tobychui/The-3D-Scanner-Project/Ver3/RAW pictures and video/DSC_1704.JPG

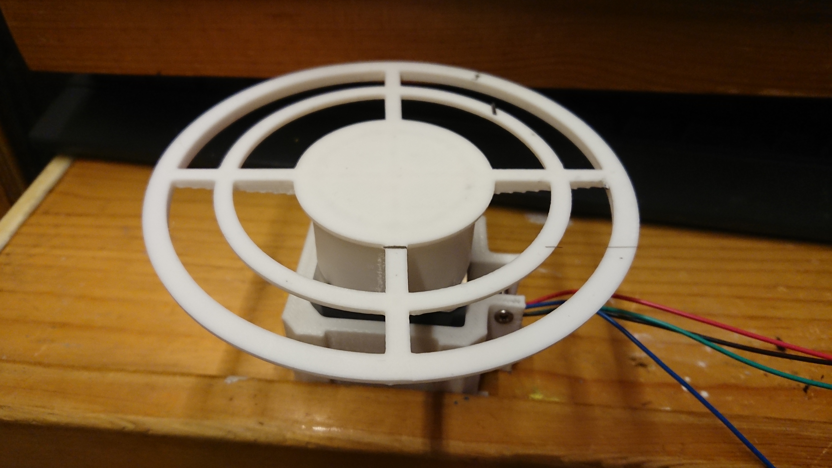
Ver3/RAW pictures and video/DSC_1704.JPG
