tobychui/The-3D-Scanner-Project/Ver3/rendering/rendering/render.307.png

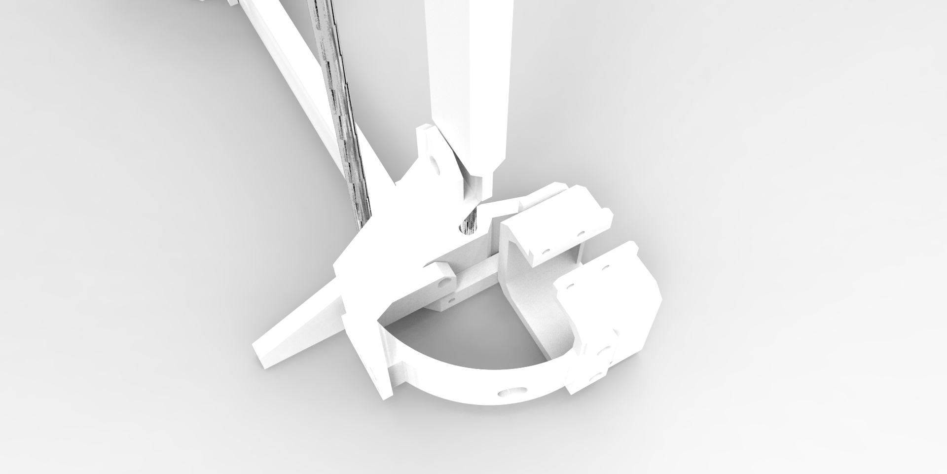
Ver3/rendering/rendering/render.307.png
