tobychui/The-3D-Scanner-Project/Ver3/trial-scan data/post-processing/2019-01-31_17-04-27.png

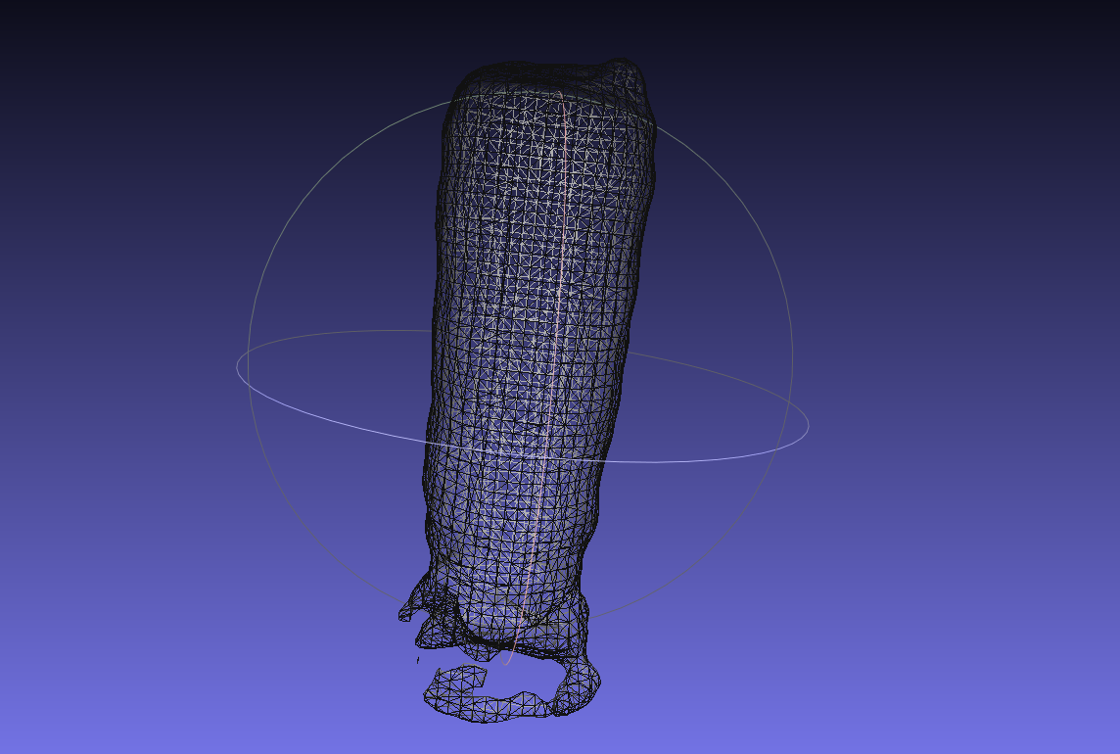
Ver3/trial-scan data/post-processing/2019-01-31_17-04-27.png
