tobychui/The-3D-Scanner-Project/Ver3/trial-scan data/post-processing/2019-01-31_17-07-32.png

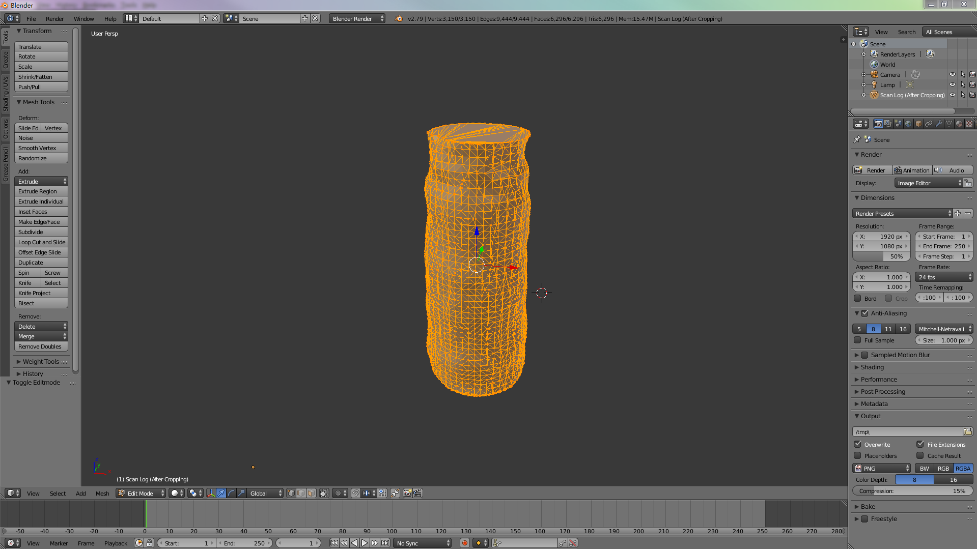
Ver3/trial-scan data/post-processing/2019-01-31_17-07-32.png
