tobychui/The-3D-Scanner-Project/Ver3/trial-scan data/post-processing/org.png

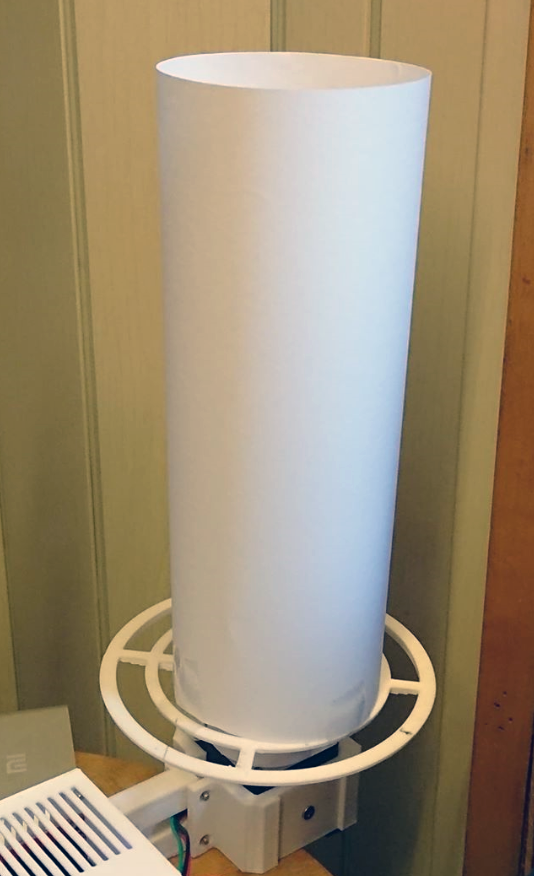
Ver3/trial-scan data/post-processing/org.png
