tobychui/The-3D-Scanner-Project/Ver3/3D Models/col support base.stl

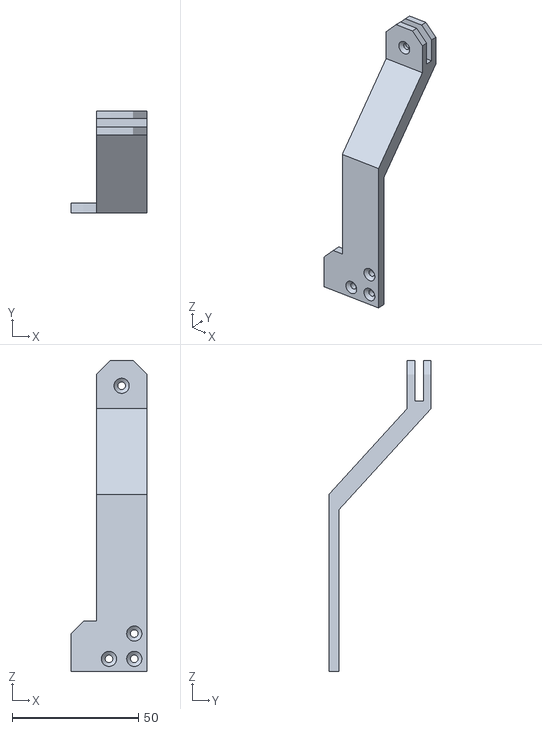
[picture p48: CAD file, 2019-02-15]
Ver3/3D Models/col support base.stl
30.0 x 40.5 x 123.0
