tobychui/The-3D-Scanner-Project/Ver3/3D Models/z-col pully sys/Bottom pully rack.stl

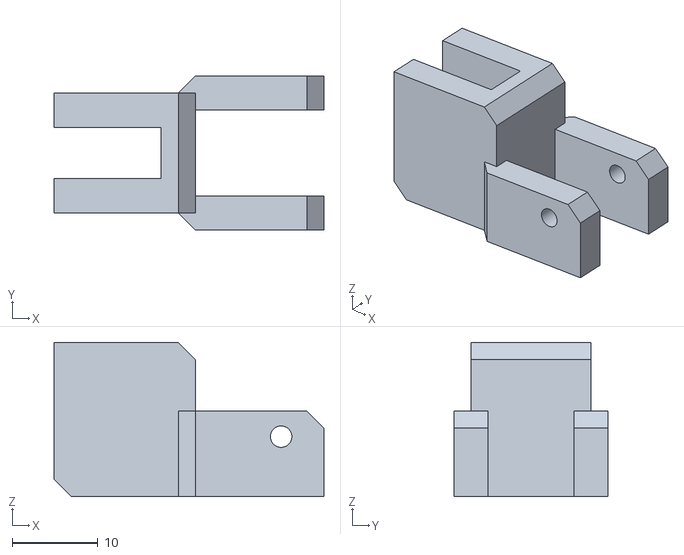
[picture p49: CAD file, 2019-02-15]
Ver3/3D Models/z-col pully sys/Bottom pully rack.stl
31.5 x 18.0 x 18.0
