tobychui/The-3D-Scanner-Project/Ver3/3D Models/z-col pully sys/Top pully rack.stl

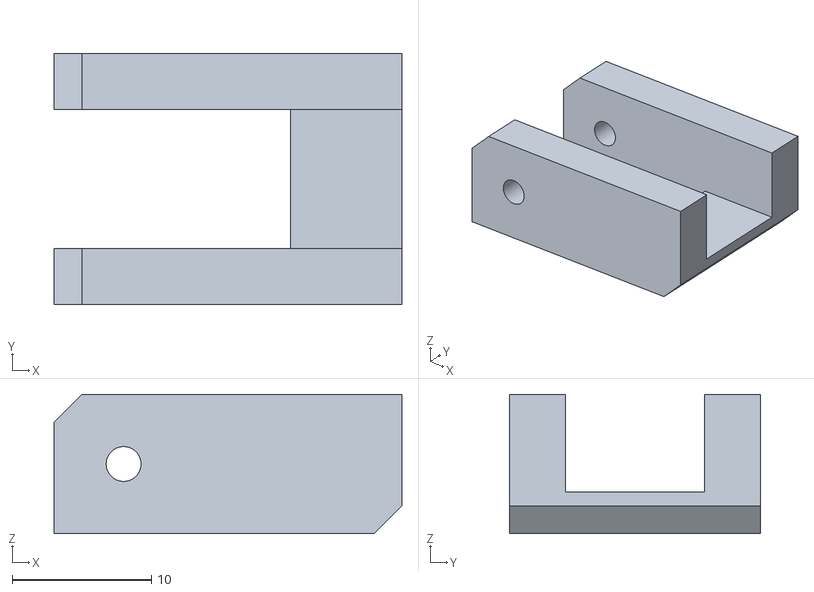
[picture p50: CAD file, 2019-02-15]
Ver3/3D Models/z-col pully sys/Top pully rack.stl
25.0 x 18.0 x 10.0
