tobychui/The-3D-Scanner-Project/Ver3/3D Models/z-stepper support arm test 1.stl

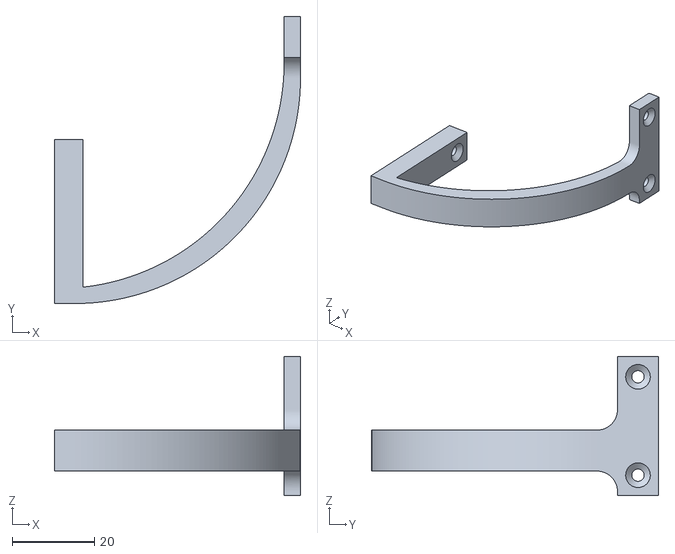
[picture p51: CAD file, 2019-02-15]
Ver3/3D Models/z-stepper support arm test 1.stl
60.0 x 70.0 x 34.0
