tobychui/The-3D-Scanner-Project/Ver3/3D Models/Stepper mount v1.stl

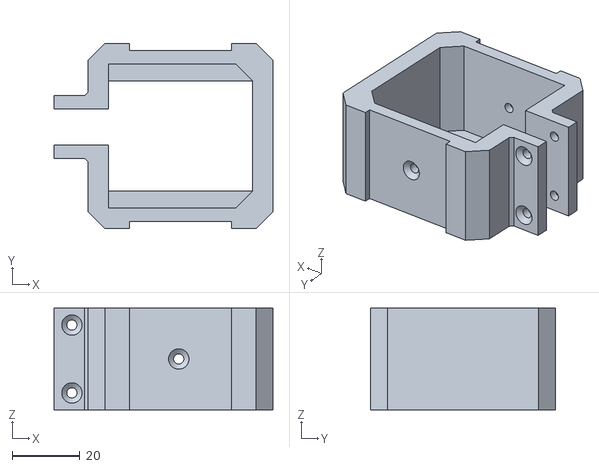
[picture p52: CAD file, 2019-02-15]
Ver3/3D Models/Stepper mount v1.stl
64.5 x 54.5 x 30.0
