tobychui/The-3D-Scanner-Project/Ver3/3D Models/Z-stepper connector.stl

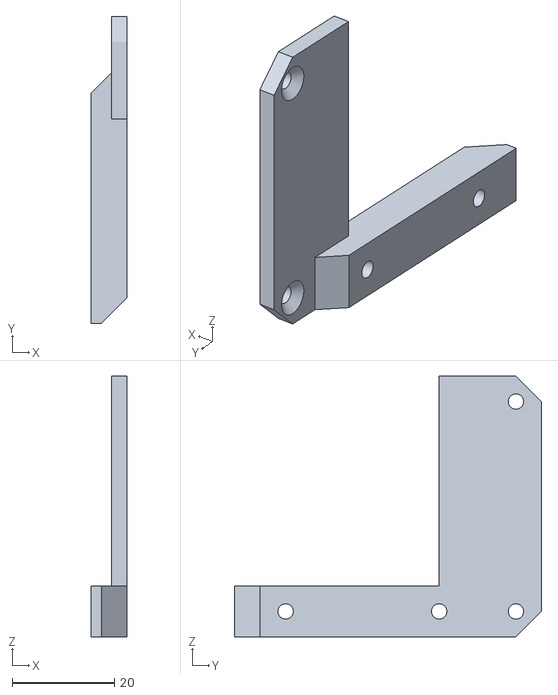
[picture p53: CAD file, 2019-02-15]
Ver3/3D Models/Z-stepper connector.stl
7.00 x 60.0 x 51.0
