tobychui/The-3D-Scanner-Project/Ver3/3D Models/z-stepper holder.stl

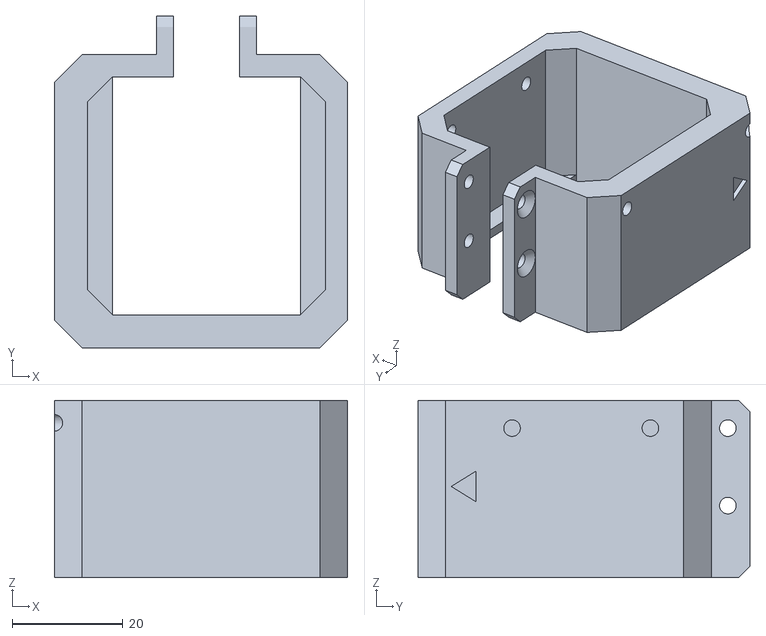
[picture p54: CAD file, 2019-02-15]
Ver3/3D Models/z-stepper holder.stl
53.0 x 60.0 x 32.0
