tobychui/The-3D-Scanner-Project/Ver3/3D Models/Dummy rod.stl

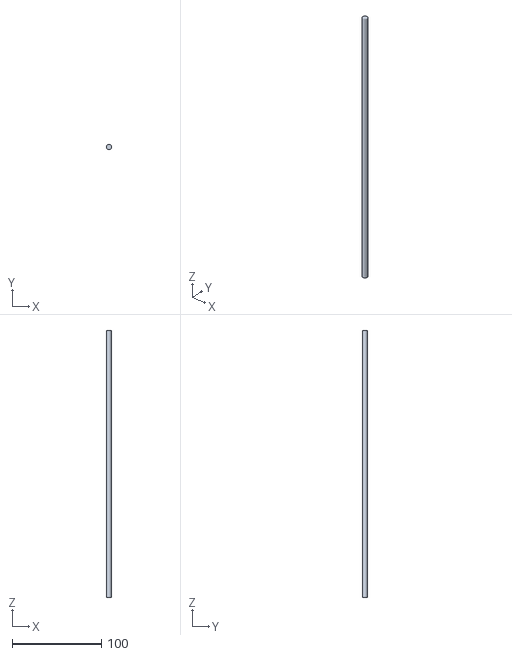
[picture p55: CAD file, 2019-02-15]
Ver3/3D Models/Dummy rod.stl
6.00 x 6.00 x 300.0
