tobychui/The-3D-Scanner-Project/Ver3/3D Models/Col support top.stl

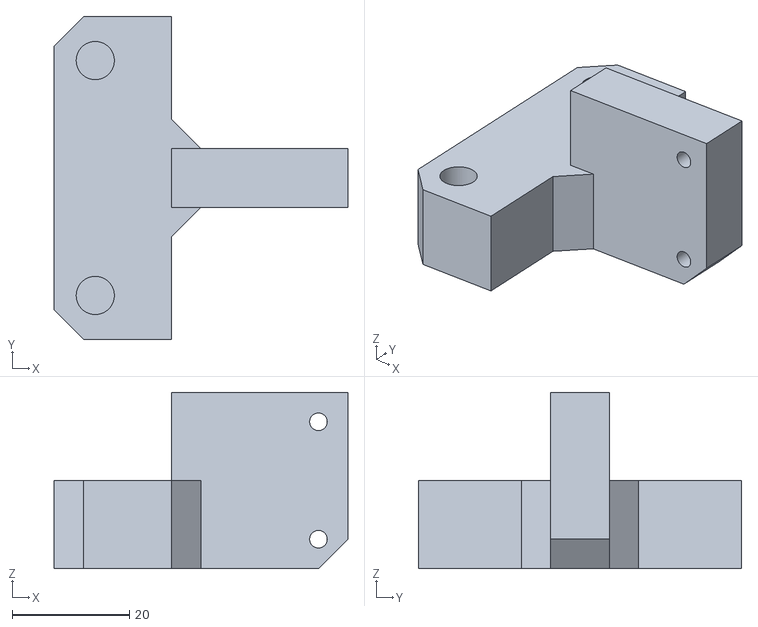
[picture p56: CAD file, 2019-02-15]
Ver3/3D Models/Col support top.stl
50.0 x 55.0 x 30.0
