tobychui/The-3D-Scanner-Project/Ver3/3D Models/Upper Support beam v2.stl

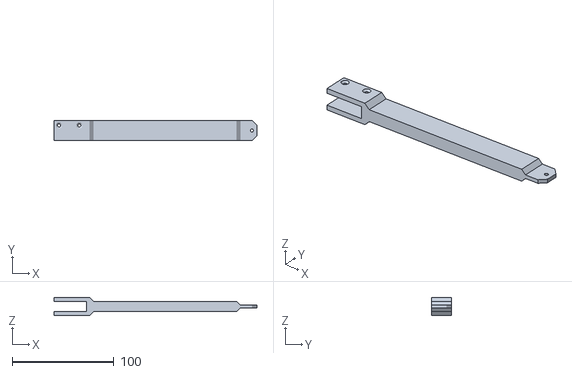
[picture p57: CAD file, 2019-02-15]
Ver3/3D Models/Upper Support beam v2.stl
200.0 x 20.0 x 18.0
